mrRobot62/depr_PODRacer/src/main/OpticalFlow.cpp

#include "PID_v1.h"
#include "OpticalFlow.h"


OpticalFlow::OpticalFlow(uint8_t taskID, SLog *log, uint8_t cs_pin, Blackbox *bb, HardwareSerial *visBus)
  : TaskAbstract(taskID, log, bb, visBus) {
  _cs = cs_pin;
  _tname = "OFLOW";
  logger->info("initialized", _tname);
}


bool OpticalFlow::begin(Receiver *receiver) {
  flow = new Bitcraze_PMW3901(_cs);
  _recv = receiver;


  if (_recv == nullptr) {
    logger->error("no receiver object available", _tname);
    setError(getID(), 0x01);
    return false;
  }
  if (flow == nullptr) {
    logger->error("PMW3901 not available", _tname);
    setError(getID(), 0x02);
    return false;
  }

  sprintf(buffer, "begin() - ready | AddrRecv:%d |", (long)&receiver);
  logger->info(buffer, _tname);

  slip2RollAxis = 0.0;
  slip2RollAxis = 0.0;

  rawX = 0;
  rawY = 0;
  setPointSlipX = 0.0;
  setPointSlipY = 0.0;

  flowCounter = 0;
  //
  // PID behaviour
  // rawInX represent the input value which got by sensor
  // The PID controller try to adjust to zero for X/Y (0 means no slip/movements)
  // depends who the sensor is assembled

  if ((direction[0] == 0) || (direction[0] == 2)) {  // NORTH or EAST
                                                     // sensor is assembled in NORTH/SOUTH direction
    pidX = new PID(&slipAdjX, &slip2RollAxis, &setPointSlipX, kpOpticalFlow, kiOpticalFlow, kdOpticalFlow, DIRECT);
    pidY = new PID(&slipAdjY, &slip2PitchAxis, &setPointSlipY, kpOpticalFlow, kiOpticalFlow, kdOpticalFlow, DIRECT);
  } else if ((direction[0] == 1) || (direction[0] == 3)) {  // WEST or SOUTH
                                                            // sensor is assembled in NORTH/SOUTH direction
    pidY = new PID(&slipAdjY, &slip2RollAxis, &setPointSlipY, kpOpticalFlow, kiOpticalFlow, kdOpticalFlow, DIRECT);
    pidX = new PID(&slipAdjX, &slip2PitchAxis, &setPointSlipX, kpOpticalFlow, kiOpticalFlow, kdOpticalFlow, DIRECT);
  }

  if (pidX == nullptr || pidY == nullptr) {
    logger->error("PID controller not initialized", _tname);
    setError(getID(), 0x03);
    return false;
  }

  pidX->SetMode(AUTOMATIC);
  pidY->SetMode(AUTOMATIC);
  pidX->SetOutputLimits(-OFLOW_PID_OUTPUT_LIMIT, OFLOW_PID_OUTPUT_LIMIT);
  pidY->SetOutputLimits(-OFLOW_PID_OUTPUT_LIMIT, OFLOW_PID_OUTPUT_LIMIT);
  pidX->SetSampleTime(LOOP_TIME);
  pidY->SetSampleTime(LOOP_TIME);

  if (flow->begin() == false) {
    logger->error("flow->begin() failed", _tname);
    setError(getID(), 0x04);
    logger->printBinary("Error:", _tname, getID());
    //logger->error("Error:", false);
    //sprintf(buffer, BYTE_TO_BINARY_PATTERN, BYTE_TO_BINARY(getError()));
    //logger->print(buffer, true);
    return false;
  }

  sprintf(buffer, "OpticalFlow ready | Receiver:%d | PMW3901:%d", (long)&receiver, (long)&flow);
  logger->info(buffer, _tname);
  cnt = 0;

  resetError();
  return true;
}

/**
    update TData for this OpticalFlow sensor

  **/
void OpticalFlow::update(void) {

  /** if one gimbal is not centered, no optical flow measurement is needed **/
  /** Assumption: if a gimbal is not centered, pilot interact (like steering) and optical flow measurement should be ignored **/
  rpy[0] = _recv->isGimbalCentered(ROLL, true);
  rpy[1] = _recv->isGimbalCentered(PITCH, true);
  rpy[2] = _recv->isGimbalCentered(YAW, true);

  // only roll/pitch can remove drifting (not yaw!)
  if ((rpy[0] == false) || (rpy[1] == false)) {
#if defined(LOG_TASK_OPTICALFLOW)
    sprintf(buffer, "=> R:%4d - P:%4d - Y:%4d -- RPY:%d-%d-%d -- not centered",
            _recv->getData(ROLL),
            _recv->getData(PITCH),
            _recv->getData(YAW),
            rpy[0], rpy[1], rpy[2]);
    logger->info(buffer, _tname);
#if defined(TEST_OPTICAL_FLOW)
    cnt = 0;
    rawX = 100;
    rawY = 100;
#endif
#endif
    _bbd.data.updated = false;
    return;
  }

#if defined(TEST_OPTICAL_FLOW)
  // nur für test
  if (cnt > 30) return;
#else
  flow->readMotionCount(&rawX, &rawY);
#endif

  // flow controll algorithm
  // check flow X/Y, PID-Adjustment(X/Y), set new relative channel values
  // PID use double values and return double. so first cast value form sensor
  // remove noice

  // Value hight depends on velocity. As higher velocity as higher value
  rawX = (isInRange(rawX, -OFLOW_PMW3901_ZERO, OFLOW_PMW3901_ZERO)) ? 0 : rawX;
  rawY = (isInRange(rawY, -OFLOW_PMW3901_ZERO, OFLOW_PMW3901_ZERO)) ? 0 : rawY;

  // adjust sensor direction
  rawX = direction[1] * rawX;
  rawY = direction[2] * rawY;

  // cumulate to roll and pitch axis.
  slipAdjX += (double)rawX;
  slipAdjY += (double)rawY;

  // we just wait some time if a flow was recognizes
  // if value is greater than threshold, we try avoid this drift and set channel values for roll/pitch
  if (abs(slipAdjX) < OFLOW_SLIP_RANGE && abs(slipAdjY) < OFLOW_SLIP_RANGE) {
    return;
  }
  // note: pidXY result ist stored in slipRollAxis / slipPitchAxis
  pidY->Compute();
  pidX->Compute();

  // based on slipAdjX/Y (cumulated rawX/Y values) the PID controller calculate a
  // new adjustable value. this value is mapped is in range ob PID-Limits (SetOutputLimits(-PID_OUTPUT_LIMIT, PID_OUTPUT_LIMIT);)
  _bbd.data.ch[ROLL] = (int16_t)slip2RollAxis;
  _bbd.data.ch[PITCH] = (int16_t)slip2PitchAxis;

//_data[ROLL]
#if defined(LOG_TASK_OPTICALFLOW)
#if defined(USE_SERIAL_PLOTTER)

  sprintf(buffer, "rX:%3d, rY:%3d, Xnorm:%3d, Ynorm:%3d, sRAX:%4.2f, sRAY:%4.2f, Roll:%4d, Pitch:%4d",
          rawX, rawY,
          rawXnormalized, rawYnormalized,
          slip2RollAxis, slip2PitchAxis,
          _data.ch[ROLL], _data.ch[PITCH]);
  logger->simulate(buffer, _tname);
#else
  sprintf(buffer, "X/Y/Roll/Pitch: <%4d,%4d> <%8f,%8f> CNT(%3d)", rawX, rawY, slipX, slipY);
  logger->info(buffer, _tname);
#endif
#endif

#if defined(TEST_OPTICAL_FLOW)
  cnt++;
#endif

  flowCounter = 0;
  rawX += (int16_t)slip2RollAxis;
  rawY += (int16_t)slip2PitchAxis;

  slip2RollAxis = slip2PitchAxis = 0.0f;
  slipAdjX = slipAdjY = 0.0f;
  // set upadate flag
  setUpdateFlag();
  resetError();
}
