mrRobot62/depr_PODRacer/src/PODRacer_VSCODE_V2/src/globalvars.h

#ifndef _GLOBAL_VARS_H_
#define _GLOBAL_VARS_H_

#include <CoopTaskBase.h>
#include <CoopTask.h>

#define TASK_LIST_SIZE 10

typedef struct {
  CoopTask<void> *list[TASK_LIST_SIZE];
} TaskList;
extern TaskList taskList;


// global variables used to set via CLI
extern uint16_t ARMING_VALUE;

#endif
