mrRobot62/depr_PODRacer/src/PODRacer_VSCODE_V2/src/TaskOpticalFlow.cpp

#include "TaskOpticalFlow.h"

TaskOpticalFlow::TaskOpticalFlow(SLog *log, const char*name, uint8_t taskID, CoopSemaphore *taskSema) 
  : Task(log, name, taskID, taskSema) {

}

void TaskOpticalFlow::begin(bool allowLog) {

}

void TaskOpticalFlow::update(TaskData *data, bool allowLog) {

}
