mrRobot62/depr_PODRacer/src/PODRacer_VSCODE_V2/src/TaskBlink.cpp

#include "TaskBlink.h"

BlinkPattern::BlinkPattern(SLog *log, const char* name, uint8_t taskID, CoopSemaphore *taskSema )
  : Task(log, name, taskID, taskSema) {
  log->info("BlinkPattern initialized", true, _tname);
}

/** do some initializing stuff **/
void BlinkPattern::begin(bool allowLog) {
    reset();
    for (uint8_t i=0; i < sizeof(pins); i++) {
      pinMode(pins[i], OUTPUT);
    }
    sprintf(buffer, "begin() - task ready");
    log->info(buffer, true, _tname);
}

void BlinkPattern::update(uint8_t blinkPattern, bool allowLog) {
  cPattern = constrain(blinkPattern, 0, MAX_PATTERN-1);
  /** update() is called in our processesing loop, call current blink pattern **/
  uint8_t   SEQ = pattern[cPattern][0];       // how often blink
  uint16_t  SEQ_MS = pattern[cPattern][1];    // in this range of milliseconds
  uint16_t  ON = pattern[cPattern][2];        // blink ON in ms
  uint16_t  OFF = abs((SEQ_MS / SEQ) - ON);   // calculated OFF time in ms
  uint16_t  WAIT = pattern[cPattern][3];      // wait after SEQ_MS befor start new seq
  uint8_t   pin = pattern[cPattern][4];       // led pin
  for (uint8_t i = 0; i < SEQ; i++) {
    digitalWrite(pin, HIGH);
    delay(ON);
    digitalWrite(pin, LOW);
    delay(OFF);
  }
  digitalWrite(pin, LOW);
  delay(WAIT);
  yield();
}
